trawlergeek/Retro3DCases/SC126_Z180_StackedCase/SC126_Stacked_SSD1.8Shellv3.stl

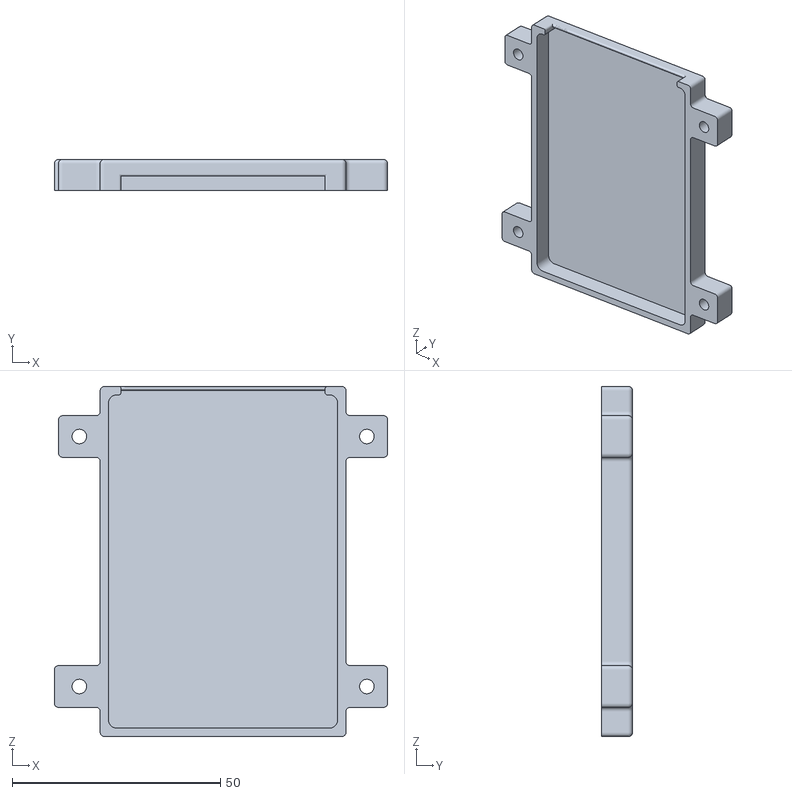
[picture p15: CAD file, 2020-10-07]
SC126_Z180_StackedCase/SC126_Stacked_SSD1.8Shellv3.stl
80.0 x 7.50 x 84.0
