trawlergeek/Retro3DCases/SC126_Z180_StackedCase/SC126_Stacked_FDD Shell.stl

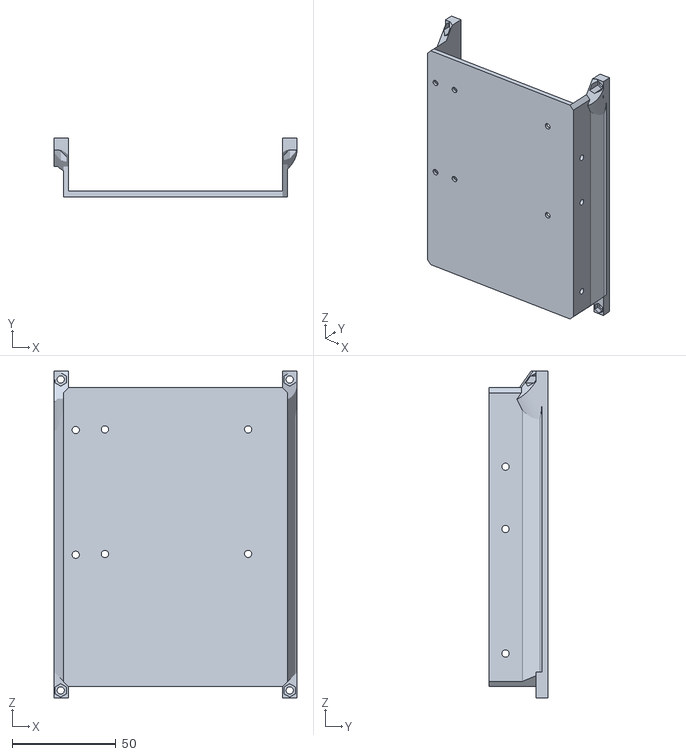
[picture p16: CAD file, 2020-10-07]
SC126_Z180_StackedCase/SC126_Stacked_FDD Shell.stl
117.0 x 28.5 x 157.5
