trawlergeek/Retro3DCases/SC126_Z180_StackedCase/SC126 _IDE_Drive_Bench_Large.stl

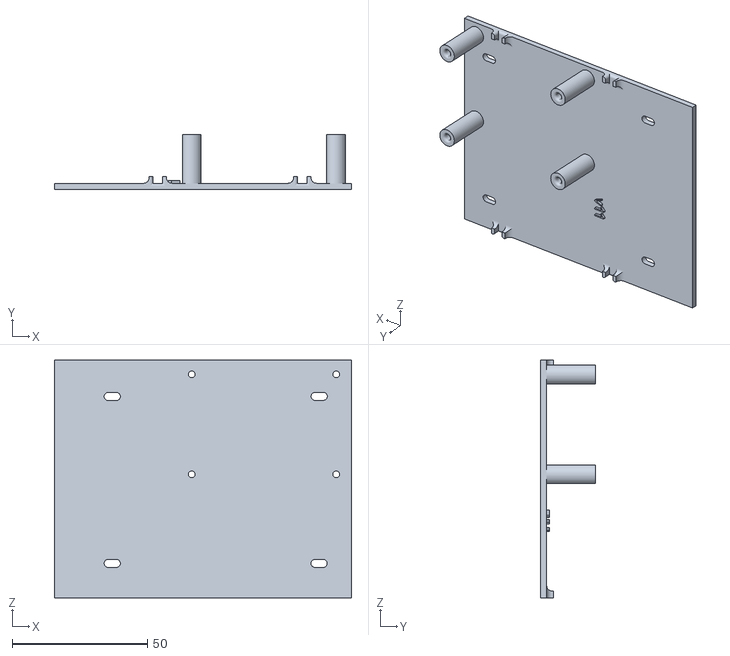
[picture p17: CAD file, 2020-10-07]
SC126_Z180_StackedCase/SC126 _IDE_Drive_Bench_Large.stl
110.0 x 20.2 x 88.0
